MazenAbou/SmartSafe/SmartSafe/SmartSafe.kicad_sch

## KiCad design SmartSafe/SmartSafe.kicad_sch (2025-03-11)

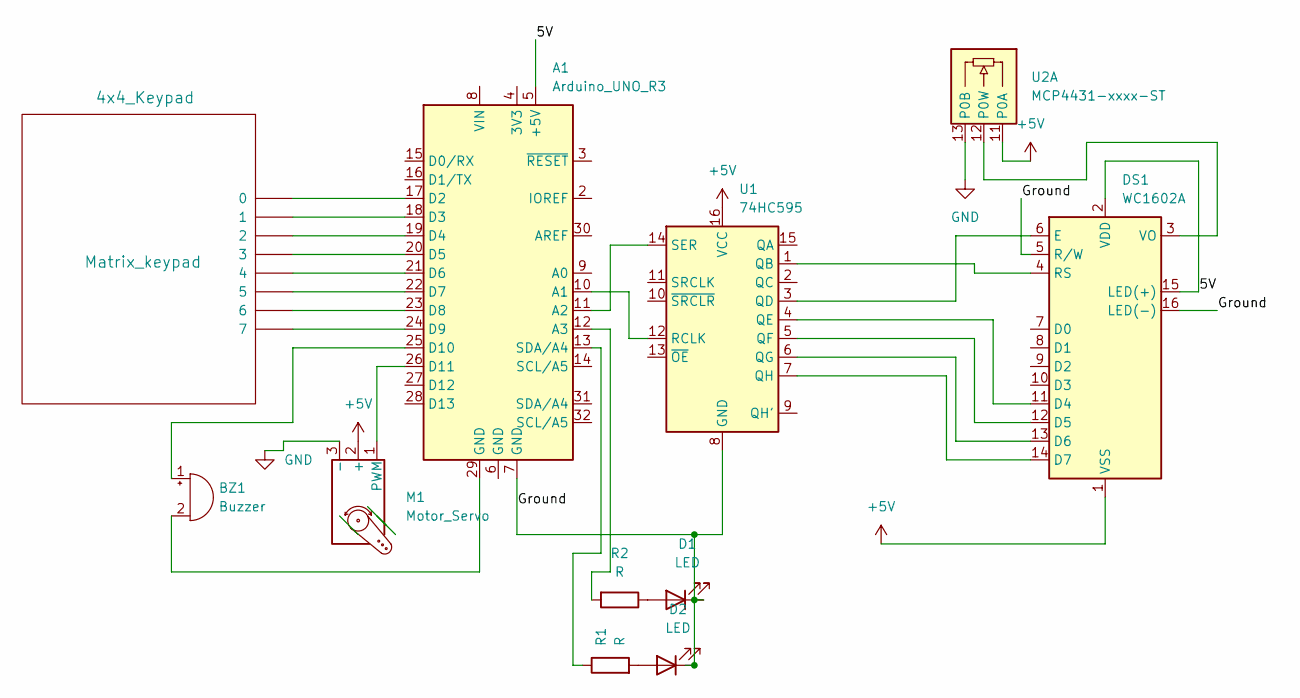
[picture p2: schematic SmartSafe.kicad_sch]

Parts:
A1: Arduino_UNO_R3
BZ1: Buzzer
D1, D2: LED
DS1: WC1602A
M1: Motor_Servo
Matrix_keypad: 4x4_Keypad
R1, R2: R
U1: 74HC595
U2: MCP4431-xxxx-ST; TSSOP-20_4.4x6.5mm_P0.65mm

Connections:
5V: A1.5 (+5V), DS1.2 (VDD), DS1.15 (LED(+))
+5V: DS1.1 (VSS), M1.2 (+), U1.16 (VCC), U2.11 (P0A)
GND: M1.3 (-), U2.13 (P0B)
Ground: A1.7 (GND), D1.1 (K), D2.1 (K), DS1.5 (R/W), DS1.16 (LED(-)), U1.8 (GND)
unnamed: A1.10 (A1), U1.12 (RCLK)
unnamed: A1.11 (A2), U1.14 (SER)
unnamed: A1.12 (A3), R2.2
unnamed: A1.13 (SDA/A4), R1.1
unnamed: A1.17 (D2), Matrix_keypad.~
unnamed: A1.18 (D3), Matrix_keypad.~
unnamed: A1.19 (D4), Matrix_keypad.~
unnamed: A1.20 (D5), Matrix_keypad.~
unnamed: A1.21 (D6), Matrix_keypad.~
unnamed: A1.22 (D7), Matrix_keypad.~
unnamed: A1.23 (D8), Matrix_keypad.~
unnamed: A1.24 (D9), Matrix_keypad.~
unnamed: A1.25 (D10), BZ1.1 (+)
unnamed: A1.26 (D11), M1.1 (PWM)
unnamed: A1.29 (GND), BZ1.2 (-)
unnamed: D1.2 (A), R2.1
unnamed: D2.2 (A), R1.2
unnamed: DS1.3 (VO), U2.12 (P0W)
unnamed: DS1.4 (RS), U1.1 (QB)
unnamed: DS1.6 (E), U1.3 (QD)
unnamed: DS1.11 (D4), U1.4 (QE)
unnamed: DS1.12 (D5), U1.5 (QF)
unnamed: DS1.13 (D6), U1.6 (QG)
unnamed: DS1.14 (D7), U1.7 (QH)
